re-innovation/6_LED_Display/6_LED_Display_PCB_files/LED_Display_SPI_AS1107_28_11_13.sch

## KiCad design 6_LED_Display_PCB_files/LED_Display_SPI_AS1107_28_11_13.sch (2013-12-25)

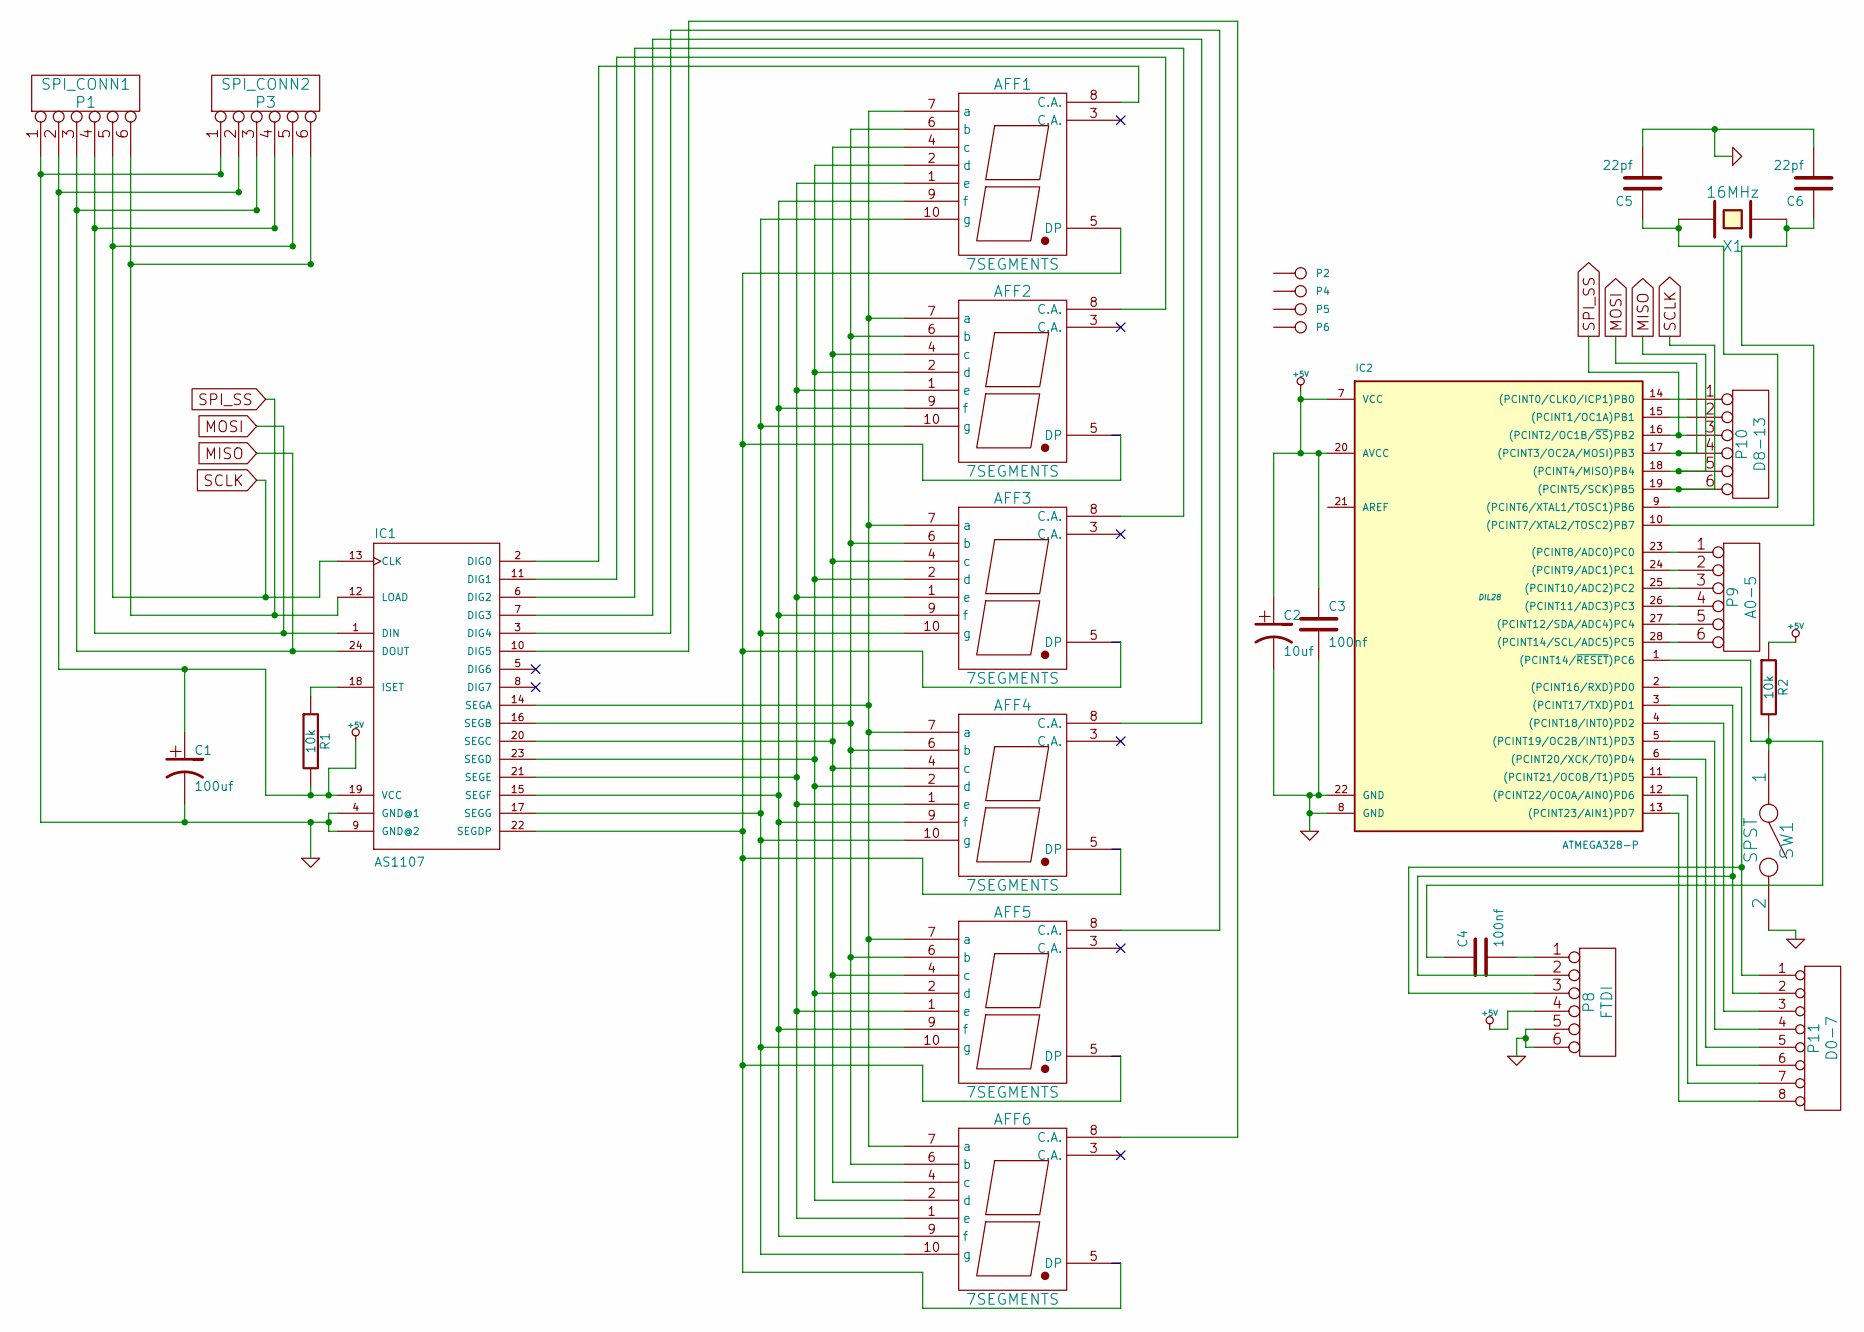
[picture p1: schematic LED_Display_SPI_AS1107_28_11_13.sch]

Parts:
AFF1, AFF2, AFF3, AFF4, AFF5, AFF6: 7SEGMENTS
C1: 100uf
C2: 10uf
C3, C4: 100nf
C5, C6: 22pf
IC1: AS1107; maxim-10-DIL24-3
IC2: ATMEGA328-P; DIL28
P1: SPI_CONN1
P2, P4, P5, P6: CONN_1
P3: SPI_CONN2
P8: FTDI
P9: A0-5
P10: D8-13
P11: D0-7
R1, R2: 10k
SW1: SPST
X1: 16MHz

Connections:
+5V: C1.1, C2.1, C3.1, IC1.19 (VCC), IC2.7 (VCC), IC2.20 (AVCC), P1.2, P3.2, P8.4, R1.2, R2.1
GND: C1.2, C2.2, C3.2, C5.2, C6.2, IC1.4 (GND@1), IC1.9 (GND@2), IC2.8 (GND), IC2.22 (GND), P1.1, P3.1, P8.5, P8.6, SW1.2
MISO: IC1.24 (DOUT), IC2.18 ((PCINT4/MISO)PB4), P1.3, P3.3, P10.5
MOSI: IC1.1 (DIN), IC2.17 ((PCINT3/OC2A/MOSI)PB3), P1.4, P3.4, P10.4
unnamed: AFF1.1 (e), AFF2.1 (e), AFF3.1 (e), AFF4.1 (e), AFF5.1 (e), AFF6.1 (e), IC1.21 (SEGE)
unnamed: AFF1.2 (d), AFF2.2 (d), AFF3.2 (d), AFF4.2 (d), AFF5.2 (d), AFF6.2 (d), IC1.23 (SEGD)
unnamed: AFF1.4 (c), AFF2.4 (c), AFF3.4 (c), AFF4.4 (c), AFF5.4 (c), AFF6.4 (c), IC1.20 (SEGC)
unnamed: AFF1.5 (DP), AFF2.5 (DP), AFF3.5 (DP), AFF4.5 (DP), AFF5.5 (DP), AFF6.5 (DP), IC1.22 (SEGDP)
unnamed: AFF1.6 (b), AFF2.6 (b), AFF3.6 (b), AFF4.6 (b), AFF5.6 (b), AFF6.6 (b), IC1.16 (SEGB)
unnamed: AFF1.7 (a), AFF2.7 (a), AFF3.7 (a), AFF4.7 (a), AFF5.7 (a), AFF6.7 (a), IC1.14 (SEGA)
unnamed: AFF1.8 (C.A.), IC1.2 (DIG0)
unnamed: AFF1.9 (f), AFF2.9 (f), AFF3.9 (f), AFF4.9 (f), AFF5.9 (f), AFF6.9 (f), IC1.15 (SEGF)
unnamed: AFF1.10 (g), AFF2.10 (g), AFF3.10 (g), AFF4.10 (g), AFF5.10 (g), AFF6.10 (g), IC1.17 (SEGG)
unnamed: AFF2.8 (C.A.), IC1.11 (DIG1)
unnamed: AFF3.8 (C.A.), IC1.6 (DIG2)
unnamed: AFF4.8 (C.A.), IC1.7 (DIG3)
unnamed: AFF5.8 (C.A.), IC1.3 (DIG4)
unnamed: AFF6.8 (C.A.), IC1.10 (DIG5)
unnamed: C4.1, IC2.1 ((PCINT14/~RESET~)PC6), R2.2, SW1.1
unnamed: C4.2, P8.1
unnamed: C5.1, IC2.9 ((PCINT6/XTAL1/TOSC1)PB6), X1.2
unnamed: C6.1, IC2.10 ((PCINT7/XTAL2/TOSC2)PB7), X1.1
unnamed: IC1.18 (ISET), R1.1
unnamed: IC2.2 ((PCINT16/RXD)PD0), P8.3, P11.1
unnamed: IC2.3 ((PCINT17/TXD)PD1), P8.2, P11.2
unnamed: IC2.4 ((PCINT18/INT0)PD2), P11.3
unnamed: IC2.5 ((PCINT19/OC2B/INT1)PD3), P11.4
unnamed: IC2.6 ((PCINT20/XCK/T0)PD4), P11.5
unnamed: IC2.11 ((PCINT21/OC0B/T1)PD5), P11.6
unnamed: IC2.12 ((PCINT22/OC0A/AIN0)PD6), P11.7
unnamed: IC2.13 ((PCINT23/AIN1)PD7), P11.8
unnamed: IC2.14 ((PCINT0/CLKO/ICP1)PB0), P10.1
unnamed: IC2.15 ((PCINT1/OC1A)PB1), P10.2
unnamed: IC2.23 ((PCINT8/ADC0)PC0), P9.1
unnamed: IC2.24 ((PCINT9/ADC1)PC1), P9.2
unnamed: IC2.25 ((PCINT10/ADC2)PC2), P9.3
unnamed: IC2.26 ((PCINT11/ADC3)PC3), P9.4
unnamed: IC2.27 ((PCINT12/SDA/ADC4)PC4), P9.5
unnamed: IC2.28 ((PCINT14/SCL/ADC5)PC5), P9.6
SCLK: IC1.13 (CLK), IC2.19 ((PCINT5/SCK)PB5), P1.5, P3.5, P10.6
SPI_SS: IC1.12 (LOAD), IC2.16 ((PCINT2/OC1B/~SS~)PB2), P1.6, P3.6, P10.3
